Jana-Marie/haj-coaster/artwork/20210515/color.png

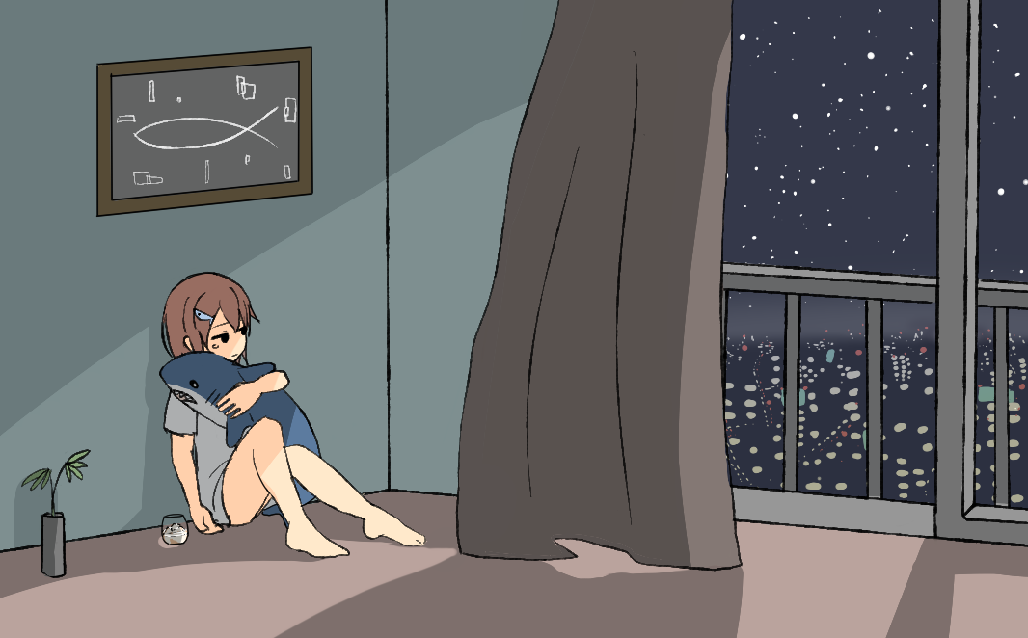
artwork/20210515/color.png
