Jana-Marie/haj-coaster/artwork/20210515/full.png

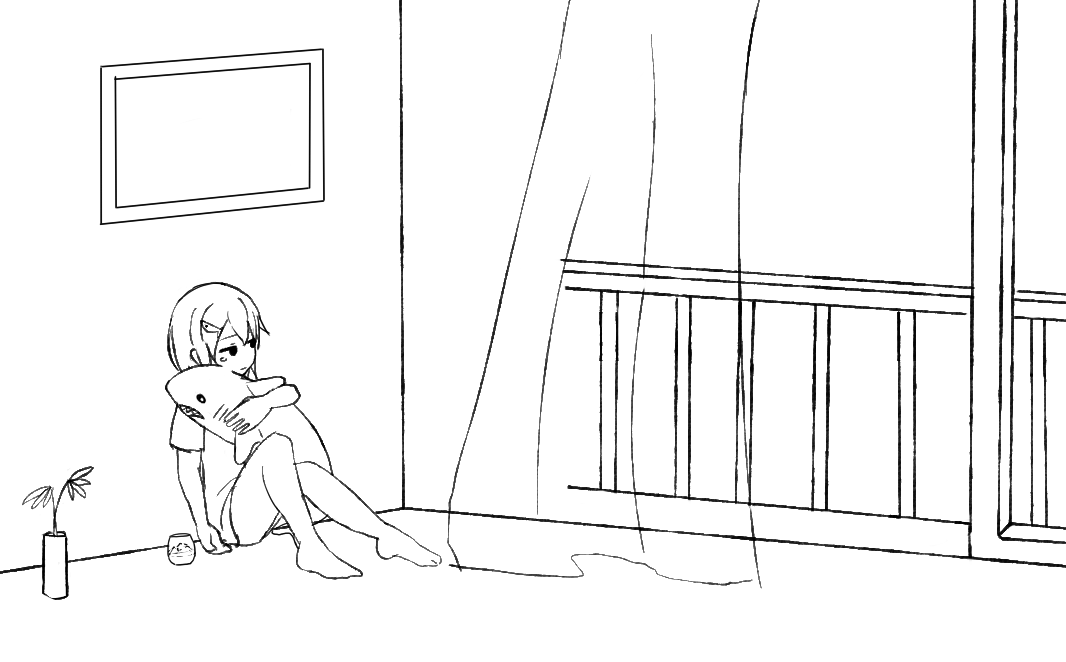
artwork/20210515/full.png
