Jana-Marie/haj-coaster/artwork/20210515/line.png

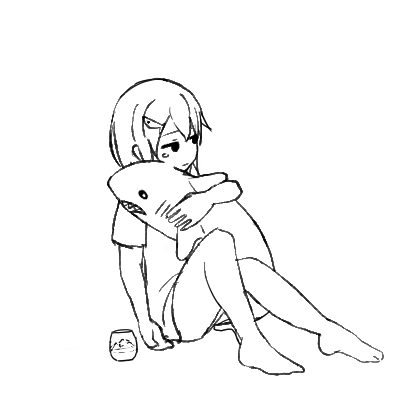
artwork/20210515/line.png
