Jana-Marie/haj-coaster/artwork/lineart_pcb.png

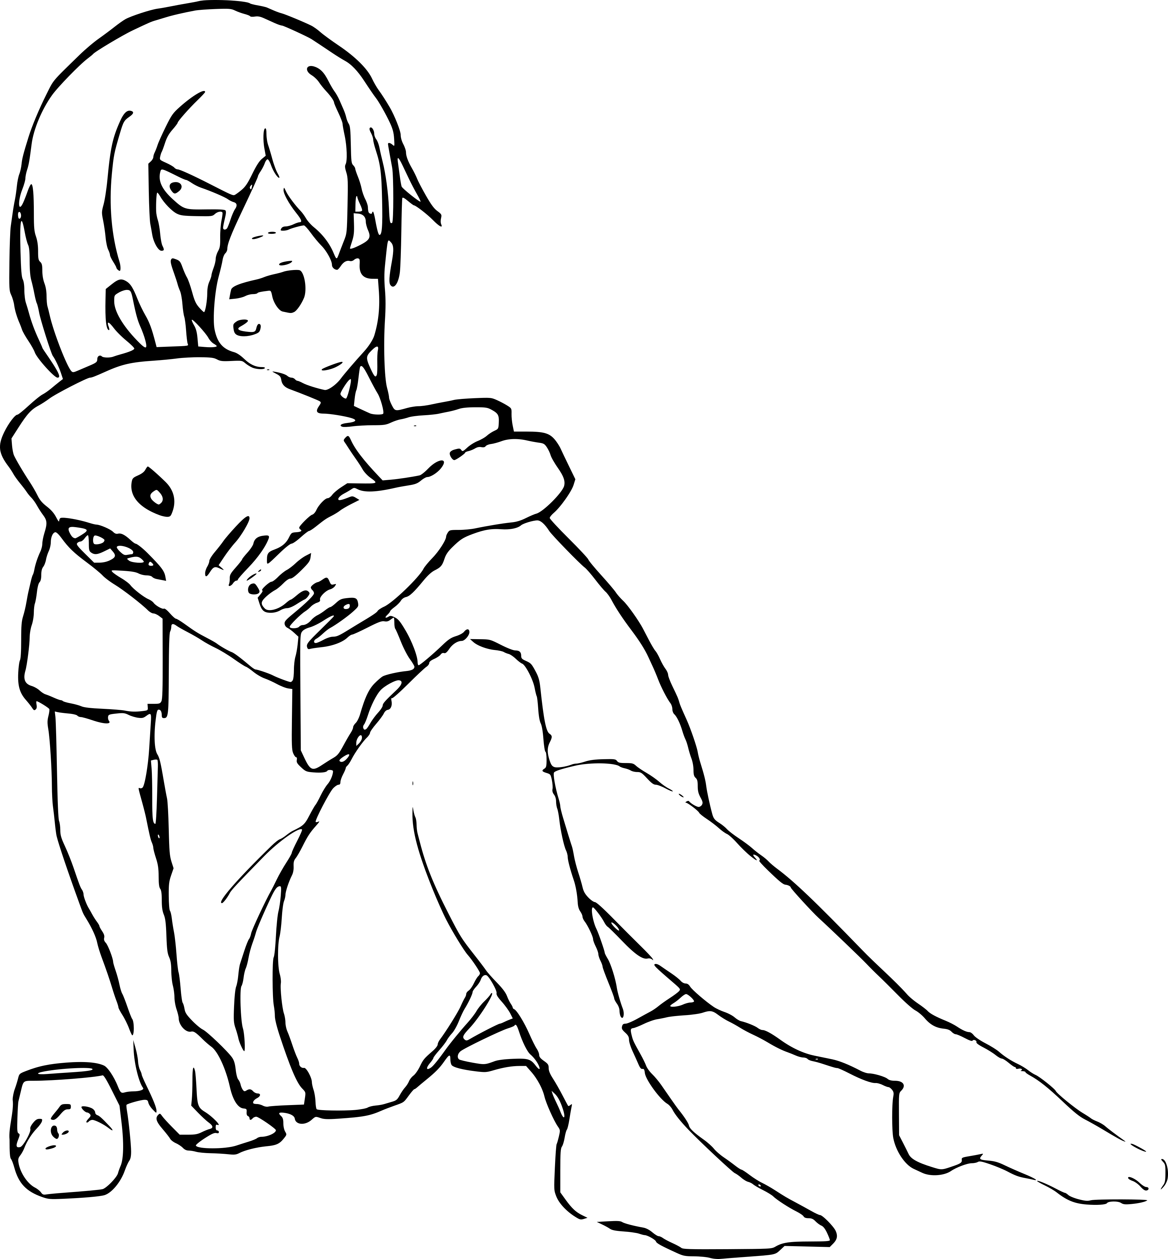
artwork/lineart_pcb.png
