Jana-Marie/haj-coaster/artwork/out1.png

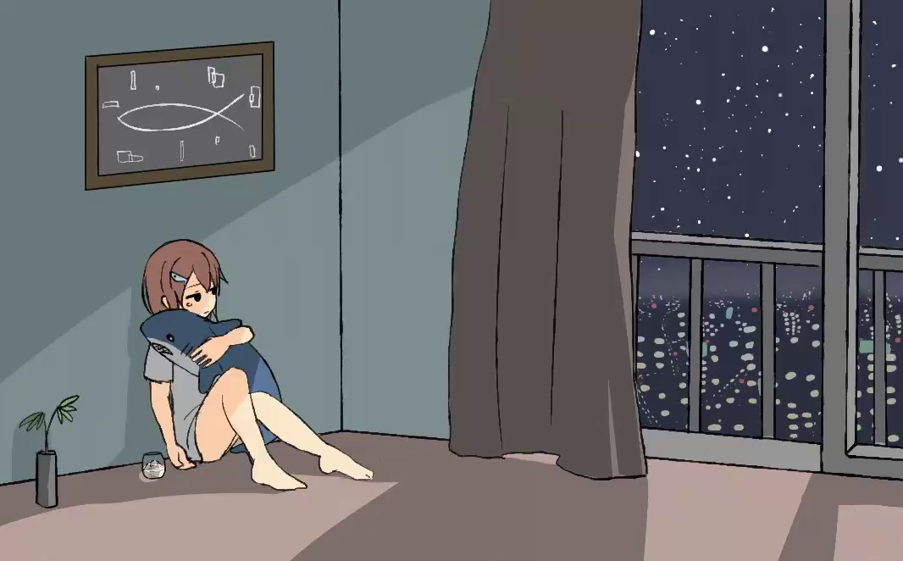
artwork/out1.png
