Jana-Marie/haj-coaster/artwork/out3.png

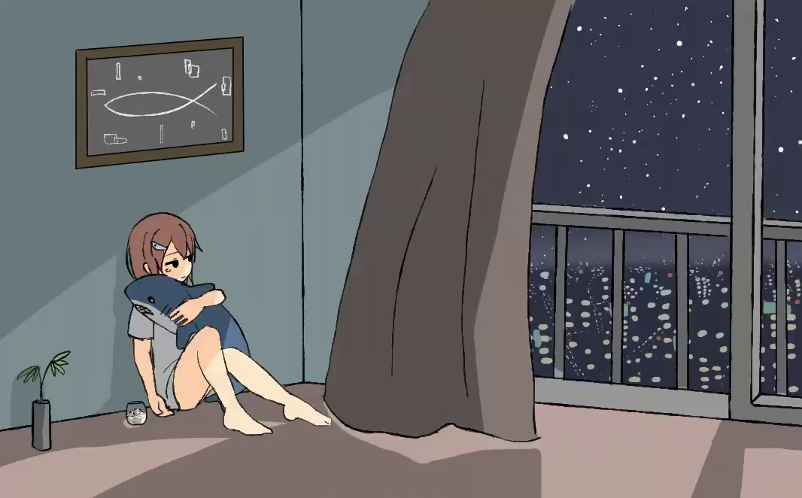
artwork/out3.png
