Jana-Marie/haj-coaster/artwork/out4.png

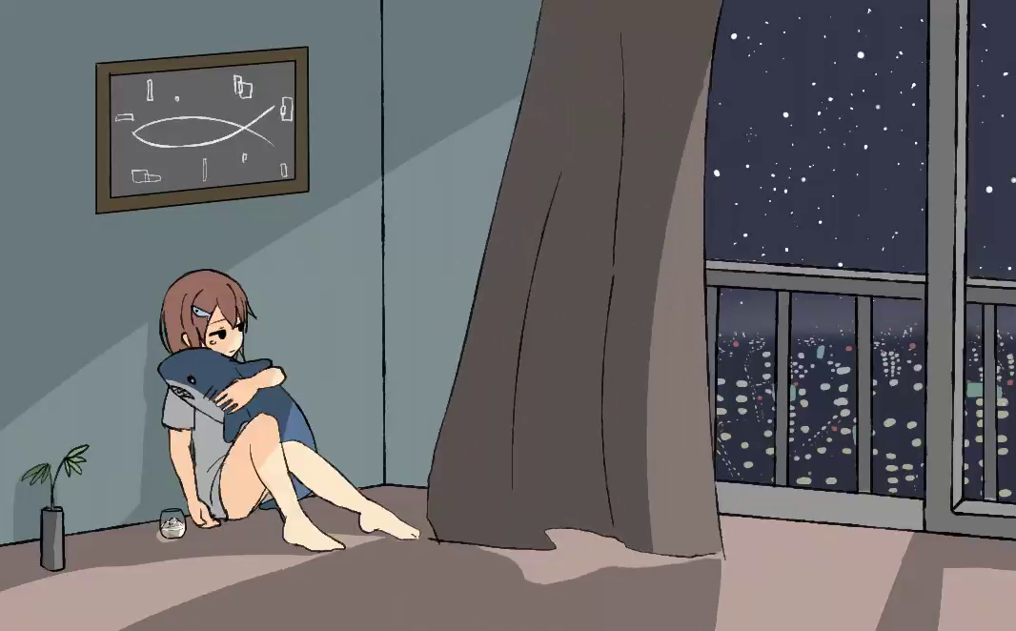
artwork/out4.png
