Jana-Marie/haj-coaster/artwork/stars.png

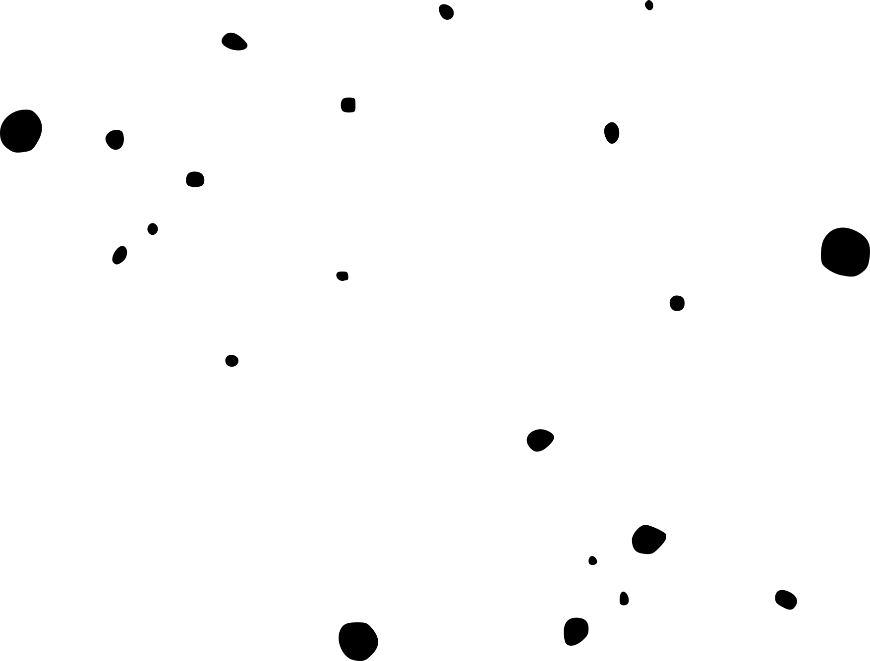
artwork/stars.png
